Emile666/THD_Analyzer/eep.c

/*==================================================================
  File Name    : eep.c
  Author       : Emile
  ------------------------------------------------------------------
  Purpose : This files contains the EEPROM related functions 
            for the STM8 uC.
  ------------------------------------------------------------------
  This is free software: you can redistribute it and/or modify
  it under the terms of the GNU General Public License as published by
  the Free Software Foundation, either version 3 of the License, or
  (at your option) any later version.
 
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
  You should have received a copy of the GNU General Public License
  along with this file.  If not, see <http://www.gnu.org/licenses/>.
  ==================================================================*/ 
#include "eep.h"
#include "stm8s105.h"

/*-----------------------------------------------------------------------------
  Purpose  : This function reads a byte value from the STM8 EEPROM.
  Variables: eeprom_address: the byte address within the EEPROM. 
  Returns  : the byte value read from eeprom
  ---------------------------------------------------------------------------*/
uint8_t eeprom_read_byte(uint8_t eeprom_address)
{
    uint8_t *address = EEP_BASE_ADDR; //  EEPROM base address.
    
    address += eeprom_address;  // convert to byte-address in EEPROM
    return *(uint8_t *)address; // return result
} // eeprom_read_byte()

/*-----------------------------------------------------------------------------
  Purpose  : This function writes a (8-bit) value to the STM8 EEPROM.
  Variables: eeprom_address: the byte address within the EEPROM.
             data          : a byte value to write to the EEPROM
  Returns  : -
  ---------------------------------------------------------------------------*/
void eeprom_write_byte(uint8_t eeprom_address, uint8_t data)
{
    uint8_t *address = EEP_BASE_ADDR; //  EEPROM base address.
    uint8_t *pf      = (uint8_t *)&data;
    
    // Avoid unnecessary EEPROM writes
    if (data == eeprom_read_byte(eeprom_address)) return;
    address += eeprom_address; // convert to byte-address in EEPROM

    FLASH_DUKR = 0xae; // unlock EEPROM
    FLASH_DUKR = 0x56;
    while (!FLASH_IAPSR_DUL) ; // wait until EEPROM is unlocked
    *address   = *pf;          // write byte to eeprom
    FLASH_IAPSR_DUL = 0;       // write-protect EEPROM again
} // eeprom_write_byte()

/*-----------------------------------------------------------------------------
  Purpose  : This function reads a float value from the STM8 EEPROM.
  Variables: eeprom_address: the byte address within the EEPROM. 
  Returns  : the float value read from eeprom
  ---------------------------------------------------------------------------*/
float eeprom_read_float(uint8_t eeprom_address)
{
    uint8_t *address = EEP_BASE_ADDR; //  EEPROM base address.
    
    address += eeprom_address; // convert to byte-address in EEPROM
    return *(float *)address;  // return result
} // eeprom_read_float()

/*-----------------------------------------------------------------------------
  Purpose  : This function writes a (16-bit) value to the STM8 EEPROM.
  Variables: eeprom_address: the byte address within the EEPROM.
             data          : a float value to write to the EEPROM
  Returns  : -
  ---------------------------------------------------------------------------*/
void eeprom_write_float(uint8_t eeprom_address, float data)
{
    uint8_t *address = EEP_BASE_ADDR; //  EEPROM base address.
    uint8_t *pf      = (uint8_t *)&data;
    
    // Avoid unnecessary EEPROM writes
    if (data == eeprom_read_float(eeprom_address)) return;
    address += eeprom_address; // convert to byte-address in EEPROM

    FLASH_DUKR = 0xae; // unlock EEPROM
    FLASH_DUKR = 0x56;
    while (!FLASH_IAPSR_DUL) ; // wait until EEPROM is unlocked
    *address++ = *pf++; // write 1st byte of float
    *address++ = *pf++; // write 2nd byte of float
    *address++ = *pf++; // write 3rd byte of float
    *address   = *pf;   // write 4th byte of float
    FLASH_IAPSR_DUL = 0;                     // write-protect EEPROM again
} // eeprom_write_config()
